ipmgroup/manta50-80/3D_MODELS/RESC1608X55N.stp

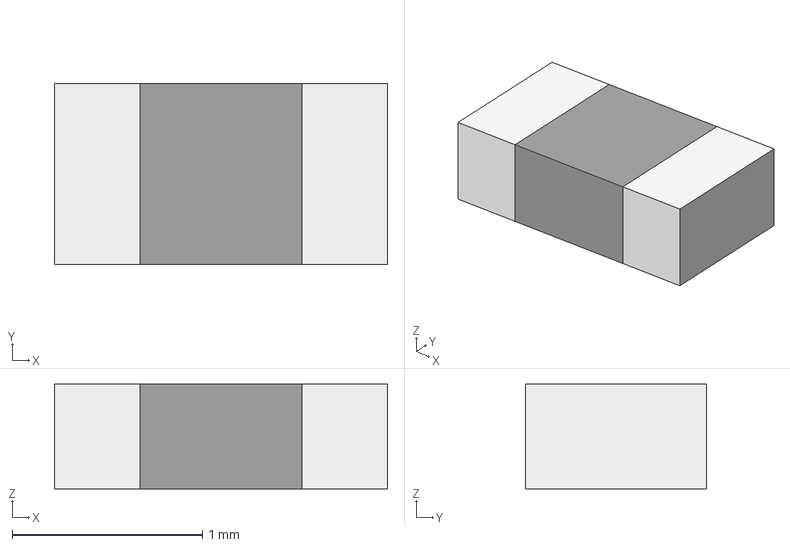
[picture p15: CAD file, 2023-11-23]
3D_MODELS/RESC1608X55N.stp
1.75 x 0.95 x 0.55 mm
