ipmgroup/manta50-80/3D_MODELS/SOT23-6-2.STEP

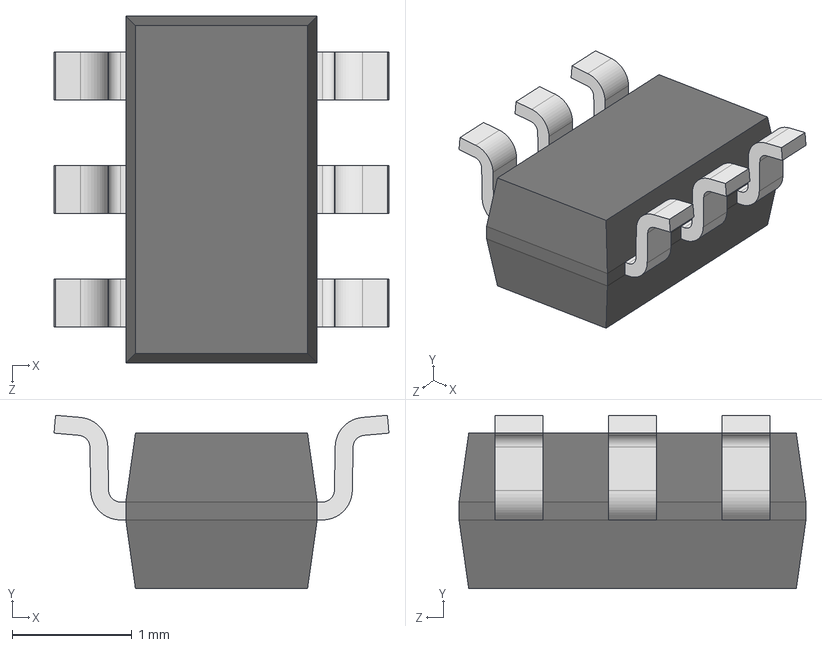
[picture p16: CAD file, 2023-11-23]
3D_MODELS/SOT23-6-2.STEP
2.80 x 1.45 x 2.90 mm
