ipmgroup/manta50-80/3D_MODELS/Honeywell HIH-5031-1.STEP

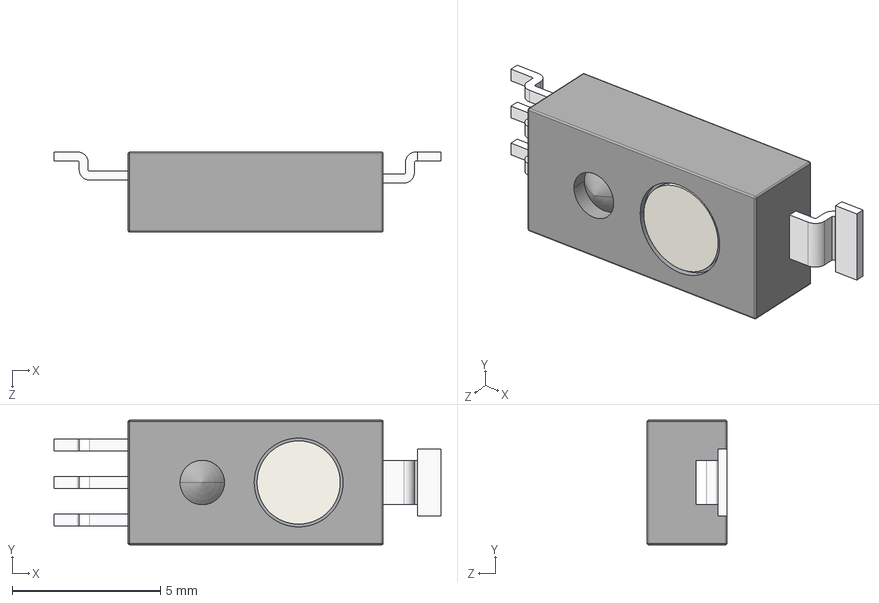
[picture p17: CAD file, 2023-11-23]
3D_MODELS/Honeywell HIH-5031-1.STEP
13.1 x 4.20 x 2.70 mm
