ipmgroup/manta50-80/3D_MODELS/SOT23.STEP

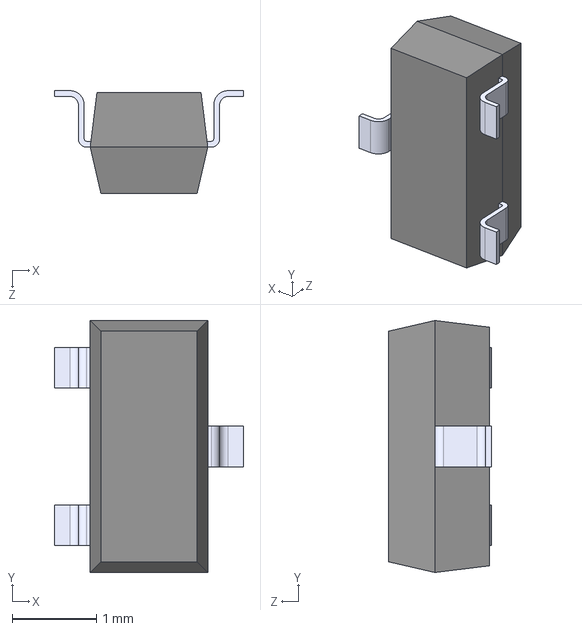
[picture p18: CAD file, 2023-11-23]
3D_MODELS/SOT23.STEP
2.25 x 3.00 x 1.22 mm
